Siddardth7/SAMPE-Fuselage-Competition/images/autoclave.jpg

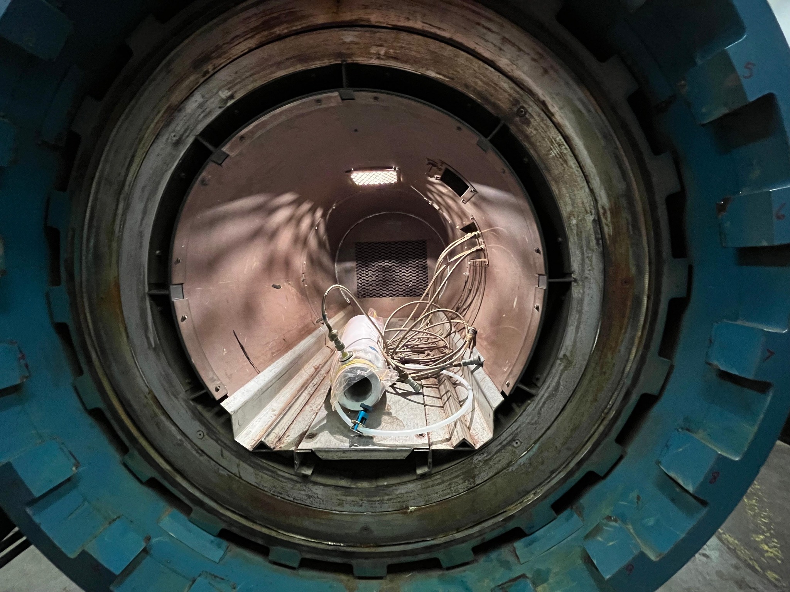
images/autoclave.jpg
