Siddardth7/SAMPE-Fuselage-Competition/images/3pt_bending_test.png

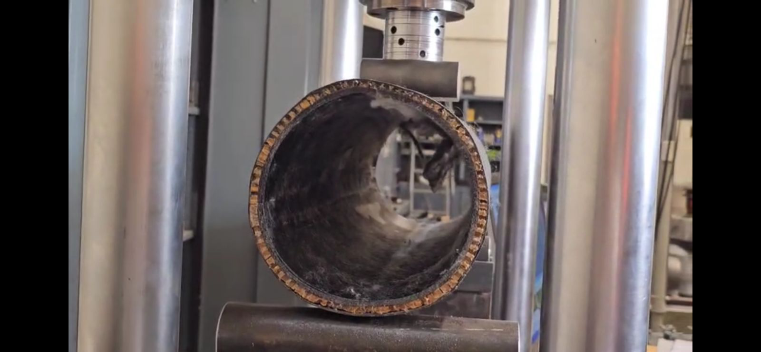
images/3pt_bending_test.png
